yuki771555/2dosui/twodosumi/web.py

from __future__ import annotations

from dataclasses import asdict
import os
from pathlib import Path
import subprocess
import sys
from typing import Any, Callable

from .cli import calibrate_scale_file, calibrate_zero_file
from .config import (
    AppConfig,
    KNOWN_EVENTS,
    ScheduledAlarmConfig,
    Secrets,
    load_config,
    load_secrets,
    save_config,
    save_secrets,
    validate_config,
)
from .notifier import send_test_webhook
from .sensors import check_sensor
from .status import read_status


EDITABLE_CONFIG_FIELDS = {
    "log_path",
    "status_path",
    "person_weight_kg",
    "sample_interval_sec",
    "warmup_samples",
    "median_samples",
    "moving_average_window",
    "exit_ratio",
    "return_ratio",
    "monitor_sec",
    "confirm_sec",
    "data_pin",
    "clock_pin",
    "hx711_ready_timeout_sec",
    "alarm_enabled",
    "buzzer_enabled",
    "buzzer_pin",
    "buzzer_duration_sec",
    "buzzer_pulse_sec",
    "scheduled_alarm_enabled",
    "scheduled_alarms",
    "bed_recheck_minutes",
    "wake_mission_enabled",
    "wake_mission_required_off_bed_sec",
    "webhook_enabled",
    "webhook_events",
    "webhook_payload_format",
    "webhook_timeout_sec",
}


class ProcessManager:
    def __init__(self, config_path: str, secrets_path: str) -> None:
        self.config_path = config_path
        self.secrets_path = secrets_path
        self.process: subprocess.Popen[bytes] | None = None

    def is_running(self) -> bool:
        return self.process is not None and self.process.poll() is None

    def start(self) -> None:
        if self.is_running():
            return
        command = [
            sys.executable,
            "-m",
            "twodosumi",
            "run",
            "--config",
            self.config_path,
            "--secrets",
            self.secrets_path,
        ]
        self.process = subprocess.Popen(command)

    def stop(self) -> None:
        if not self.is_running():
            self.process = None
            return
        assert self.process is not None
        self.process.terminate()
        try:
            self.process.wait(timeout=10)
        except subprocess.TimeoutExpired:
            self.process.kill()
            self.process.wait(timeout=10)
        self.process = None


def _coerce_config_value(field: str, value: Any) -> Any:
    int_fields = {"warmup_samples", "median_samples", "moving_average_window"}
    float_fields = {
        "person_weight_kg",
        "sample_interval_sec",
        "exit_ratio",
        "return_ratio",
        "monitor_sec",
        "confirm_sec",
        "hx711_ready_timeout_sec",
        "buzzer_duration_sec",
        "buzzer_pulse_sec",
        "bed_recheck_minutes",
        "wake_mission_required_off_bed_sec",
        "webhook_timeout_sec",
    }
    bool_fields = {
        "alarm_enabled",
        "buzzer_enabled",
        "scheduled_alarm_enabled",
        "wake_mission_enabled",
        "webhook_enabled",
    }
    list_fields = {"webhook_events"}

    if field in int_fields:
        return int(value)
    if field in float_fields:
        return float(value)
    if field in bool_fields:
        return bool(value)
    if field in list_fields:
        if not isinstance(value, list):
            raise ValueError(f"{field} must be a list")
        return [str(item) for item in value]
    if field == "scheduled_alarms":
        if not isinstance(value, list):
            raise ValueError("scheduled_alarms must be a list")
        return [
            ScheduledAlarmConfig(
                id=str(item.get("id", "")),
                time=str(item.get("time", "07:00")),
                enabled=bool(item.get("enabled", True)),
                label=str(item.get("label", "")),
                weekdays=[int(day) for day in item.get("weekdays", [0, 1, 2, 3, 4, 5, 6])],
            )
            for item in value
            if isinstance(item, dict)
        ]
    return str(value)


def create_app(config_path: str, secrets_path: str):
    try:
        from flask import Flask, jsonify, request
    except ImportError as exc:
        raise RuntimeError("Install Flask first: python3 -m pip install -r requirements-pi.txt") from exc

    app = Flask(__name__)
    manager = ProcessManager(config_path, secrets_path)

    def error_response(message: str, status: int = 400):
        return jsonify({"ok": False, "error": message}), status

    def require_auth(handler: Callable[..., Any]) -> Callable[..., Any]:
        def wrapped(*args: Any, **kwargs: Any) -> Any:
            secrets = load_secrets(secrets_path)
            if not secrets.web_ui_token:
                return error_response("web_ui_token is not configured", 503)
            token = request.headers.get("X-2Dosumi-Token", "")
            if token != secrets.web_ui_token:
                return error_response("unauthorized", 401)
            return handler(*args, **kwargs)

        wrapped.__name__ = handler.__name__
        return wrapped

    @app.get("/")
    def index() -> str:
        return INDEX_HTML

    @app.get("/healthz")
    def healthz():
        return jsonify({"ok": True})

    @app.get("/api/settings")
    @require_auth
    def get_settings():
        config = load_config(config_path)
        secrets = load_secrets(secrets_path)
        data = asdict(config)
        data["webhook_url"] = secrets.webhook_url
        data["web_ui_token_configured"] = bool(secrets.web_ui_token)
        data["known_events"] = sorted(KNOWN_EVENTS)
        return jsonify({"ok": True, "settings": data})

    @app.post("/api/settings")
    @require_auth
    def post_settings():
        payload = request.get_json(force=True, silent=True) or {}
        settings = payload.get("settings", payload)
        if not isinstance(settings, dict):
            return error_response("settings must be an object")

        config = load_config(config_path)
        secrets = load_secrets(secrets_path)
        for field, value in settings.items():
            if field in EDITABLE_CONFIG_FIELDS:
                setattr(config, field, _coerce_config_value(field, value))
            elif field == "webhook_url":
                secrets.webhook_url = str(value)
            elif field == "web_ui_token" and value:
                secrets.web_ui_token = str(value)

        errors = validate_config(config)
        if errors:
            return error_response("; ".join(errors))
        was_running = manager.is_running()
        if was_running:
            manager.stop()
        save_config(config_path, config)
        save_secrets(secrets_path, secrets)
        if was_running:
            manager.start()
        return jsonify({"ok": True, "restarted": was_running})

    @app.get("/api/status")
    @require_auth
    def get_status():
        config = load_config(config_path)
        status = read_status(config.status_path)
        status["managed_process_running"] = manager.is_running()
        return jsonify({"ok": True, "status": status})

    @app.post("/api/run/start")
    @require_auth
    def start_run():
        manager.start()
        return jsonify({"ok": True, "running": manager.is_running()})

    @app.post("/api/run/stop")
    @require_auth
    def stop_run():
        manager.stop()
        return jsonify({"ok": True, "running": manager.is_running()})

    @app.post("/api/calibration/zero")
    @require_auth
    def calibrate_zero():
        was_running = manager.is_running()
        if was_running:
            manager.stop()
        try:
            payload = request.get_json(force=True, silent=True) or {}
            samples = int(payload.get("samples", 30))
            zero = calibrate_zero_file(config_path, samples)
        finally:
            if was_running:
                manager.start()
        return jsonify({"ok": True, "zero_offset": zero, "restarted": was_running})

    @app.post("/api/calibration/scale")
    @require_auth
    def calibrate_scale():
        was_running = manager.is_running()
        if was_running:
            manager.stop()
        try:
            payload = request.get_json(force=True, silent=True) or {}
            samples = int(payload.get("samples", 30))
            known_kg = float(payload.get("known_kg", 0))
            scale = calibrate_scale_file(config_path, known_kg, samples)
        finally:
            if was_running:
                manager.start()
        return jsonify({"ok": True, "scale_factor": scale, "restarted": was_running})

    @app.post("/api/sensor/check")
    @require_auth
    def sensor_check():
        was_running = manager.is_running()
        if was_running:
            manager.stop()
        try:
            payload = request.get_json(force=True, silent=True) or {}
            samples = int(payload.get("samples", 10))
            interval_sec = float(payload.get("interval_sec", 0.1))
            config = load_config(config_path)
            errors = validate_config(config)
            if errors:
                return error_response("; ".join(errors))
            result = check_sensor(config, samples=samples, interval_sec=interval_sec)
        finally:
            if was_running:
                manager.start()
        return jsonify({"ok": True, "sensor": asdict(result), "restarted": was_running})

    @app.post("/api/test-webhook")
    @require_auth
    def test_webhook():
        config = load_config(config_path)
        secrets = load_secrets(secrets_path)
        if not secrets.webhook_url:
            return error_response("webhook_url is not configured")
        send_test_webhook(config, secrets)
        return jsonify({"ok": True})

    return app


def ensure_secrets_file(path: str) -> None:
    target = Path(path)
    if target.exists():
        return
    token = os.urandom(12).hex()
    save_secrets(target, Secrets(web_ui_token=token))
    print(f"Created {target} with web_ui_token={token}", flush=True)


def run_web(config_path: str, secrets_path: str, host: str, port: int) -> None:
    ensure_secrets_file(secrets_path)
    app = create_app(config_path, secrets_path)
    print(f"Open http://{host}:{port}", flush=True)
    app.run(host=host, port=port)


INDEX_HTML = r"""<!doctype html>
<html lang="ja">
<head>
  <meta charset="utf-8">
  <meta name="viewport" content="width=device-width, initial-scale=1">
  <title>2dosumi</title>
  <style>
    :root {
      color-scheme: light;
      font-family: -apple-system, BlinkMacSystemFont, "SF Pro Text", "SF Pro Display", "Segoe UI", system-ui, sans-serif;
      --bg: #f2f2f7;
      --panel: #ffffff;
      --panel-soft: #f2f2f7;
      --panel-glass: rgba(255, 255, 255, 0.78);
      --bar-glass: rgba(248, 248, 248, 0.86);
      --ink: #1d1d1f;
      --muted: #6e6e73;
      --line: rgba(60, 60, 67, 0.18);
      --accent: #007aff;
      --accent-dark: #005ecb;
      --accent-soft: rgba(0, 122, 255, 0.11);
      --good: #34c759;
      --warn: #ff3b30;
      --blue: #007aff;
      --on-accent: #ffffff;
      --shadow: 0 22px 48px rgba(0, 0, 0, 0.08);
      --button-shadow: none;
      --hero-bg: linear-gradient(180deg, rgba(255, 255, 255, 0.96), rgba(255, 255, 255, 0.82));
      --status-bg: #101828;
      --status-ink: #eef4ff;
      --surface-shadow: 0 1px 0 rgba(0, 0, 0, 0.03), 0 10px 30px rgba(0, 0, 0, 0.04);
      --segment-bg: rgba(118, 118, 128, 0.12);
      --segment-active: rgba(255, 255, 255, 0.96);
    }
    [data-theme="dark"] {
      color-scheme: dark;
      --bg: #000000;
      --panel: #1c1c1e;
      --panel-soft: #2c2c2e;
      --panel-glass: rgba(28, 28, 30, 0.82);
      --bar-glass: rgba(28, 28, 30, 0.84);
      --ink: #f5f5f7;
      --muted: #a1a1a6;
      --line: rgba(84, 84, 88, 0.58);
      --accent: #0a84ff;
      --accent-dark: #64b5ff;
      --accent-soft: rgba(10, 132, 255, 0.18);
      --good: #30d158;
      --warn: #ff453a;
      --blue: #0a84ff;
      --on-accent: #ffffff;
      --shadow: 0 24px 58px rgba(0, 0, 0, 0.5);
      --button-shadow: none;
      --hero-bg: linear-gradient(180deg, rgba(28, 28, 30, 0.96), rgba(28, 28, 30, 0.84));
      --status-bg: #111113;
      --status-ink: #f5f5f7;
      --surface-shadow: 0 1px 0 rgba(255, 255, 255, 0.04), 0 12px 34px rgba(0, 0, 0, 0.22);
      --segment-bg: rgba(118, 118, 128, 0.24);
      --segment-active: rgba(99, 99, 102, 0.86);
    }
    * { box-sizing: border-box; }
    [hidden] { display: none !important; }
    html { scroll-behavior: smooth; }
    body {
      min-height: 100vh;
      margin: 0;
      background: var(--bg);
      color: var(--ink);
      transition: background 260ms ease, color 260ms ease;
    }
    main { width: min(100%, 1180px); margin: 0 auto; padding: 18px; }
    h1, h2 { margin: 0; letter-spacing: 0; }
    h1 { font-size: clamp(30px, 5vw, 48px); line-height: 0.98; }
    h2 { font-size: 16px; }
    p { margin: 0; }
    a, button, input, select, strong, span { min-width: 0; }
    button { outline: none; }
    button:focus-visible, input:focus-visible, select:focus-visible {
      outline: 3px solid color-mix(in srgb, var(--accent) 32%, transparent);
      outline-offset: 2px;
    }
    .app-frame {
      position: relative;
      overflow: clip;
      border: 1px solid var(--line);
      border-radius: 18px;
      background: var(--panel-glass);
      box-shadow: var(--shadow);
      backdrop-filter: blur(28px) saturate(1.6);
      transition: background 260ms ease, border-color 260ms ease, box-shadow 260ms ease;
    }
    .app-frame::before { content: none; }
    .app-bar {
      position: relative;
      z-index: 1;
      display: flex;
      justify-content: space-between;
      align-items: center;
      gap: 12px;
      min-height: 64px;
      padding: 0 20px;
      border-bottom: 1px solid var(--line);
      background: var(--bar-glass);
      backdrop-filter: blur(24px) saturate(1.45);
    }
    .brand { display: flex; align-items: center; gap: 10px; min-width: 0; }
    .brand-mark {
      width: 34px;
      height: 34px;
      border-radius: 10px;
      background: linear-gradient(145deg, #5ac8fa, var(--accent));
      box-shadow: inset 0 1px 0 rgba(255, 255, 255, 0.46);
    }
    .brand-text { display: grid; gap: 2px; min-width: 0; }
    .brand strong { font-size: 17px; font-weight: 900; }
    .brand span { color: var(--muted); font-size: 12px; font-weight: 750; }
    .app-tools { display: flex; align-items: center; justify-content: flex-end; gap: 8px; min-width: 0; }
    .content { position: relative; z-index: 1; padding: 12px; }
    .tab-bar {
      position: sticky;
      top: 0;
      z-index: 4;
      display: flex;
      gap: 2px;
      padding: 3px;
      margin-bottom: 10px;
      overflow-x: auto;
      border: 0;
      border-radius: 12px;
      background: var(--segment-bg);
      backdrop-filter: blur(18px) saturate(1.45);
      scrollbar-width: none;
    }
    .tab-bar::-webkit-scrollbar { display: none; }
    .tab-button {
      display: inline-grid;
      grid-template-columns: auto auto;
      place-items: center;
      gap: 7px;
      flex: 1 1 0;
      min-width: 0;
      min-height: 44px;
      padding: 8px 14px;
      border: 0;
      border-radius: 10px;
      background: transparent;
      color: var(--muted);
      box-shadow: none;
      font-size: 13px;
      font-weight: 760;
      transition: background 180ms ease, color 180ms ease, box-shadow 180ms ease, transform 180ms ease;
    }
    .tab-button:hover { transform: none; background: color-mix(in srgb, var(--segment-active) 68%, transparent); box-shadow: none; }
    .tab-button.active {
      background: var(--segment-active);
      color: var(--ink);
      box-shadow: 0 2px 7px rgba(0, 0, 0, 0.13);
    }
    .tab-button.active .tab-icon { transform: scale(1.08); }
    .tab-icon { transition: transform 180ms cubic-bezier(.2, .9, .2, 1); }
    .theme-toggle {
      display: inline-flex;
      align-items: center;
      gap: 7px;
      min-height: 44px;
      padding: 7px 11px;
      border: 0;
      border-radius: 999px;
      background: var(--segment-bg);
      color: var(--ink);
      box-shadow: none;
      white-space: nowrap;
      backdrop-filter: blur(16px) saturate(1.35);
    }
    .theme-toggle:hover { transform: none; background: color-mix(in srgb, var(--segment-active) 72%, transparent); box-shadow: none; }
    .tab-icon { font-size: 14px; line-height: 1; }
    body:not([data-tab="overview"]) .hero { display: none; }
    .hero {
      display: grid;
      grid-template-columns: minmax(0, 1.3fr) minmax(min(100%, 220px), 0.7fr);
      gap: 14px;
      overflow: hidden;
      padding: 22px;
      border: 1px solid var(--line);
      border-radius: 18px;
      background: var(--hero-bg);
      box-shadow: var(--surface-shadow);
    }
    .hero-main { display: flex; flex-direction: column; gap: 16px; min-width: 0; }
    .hero-kicker {
      width: fit-content;
      padding: 5px 10px;
      border: 1px solid color-mix(in srgb, var(--accent) 22%, var(--line));
      border-radius: 999px;
      background: var(--accent-soft);
      color: var(--accent-dark);
      font-size: 12px;
      font-weight: 850;
    }
    .hero-state { display: flex; align-items: center; gap: 12px; flex-wrap: wrap; }
    .state-badge {
      display: inline-flex; align-items: center; gap: 9px;
      padding: 10px 18px;
      border-radius: 999px;
      font-size: clamp(20px, 3.4vw, 30px);
      font-weight: 900; line-height: 1;
      border: 1px solid var(--line);
      background: var(--panel);
      color: var(--ink);
      transition: color 200ms ease, background 200ms ease, border-color 200ms ease;
    }
    .state-badge::before {
      content: ""; width: 12px; height: 12px; border-radius: 50%;
      background: currentColor; box-shadow: 0 0 0 4px color-mix(in srgb, currentColor 22%, transparent);
    }
    .state-badge.state-idle  { color: var(--muted); }
    .state-badge.state-sleep { color: var(--accent); border-color: color-mix(in srgb, var(--accent) 40%, var(--line)); background: var(--accent-soft); }
    .state-badge.state-watch { color: #ff9f0a; border-color: color-mix(in srgb, #ff9f0a 40%, var(--line)); background: color-mix(in srgb, #ff9f0a 13%, var(--panel)); }
    .state-badge.state-alert { color: var(--warn); border-color: color-mix(in srgb, var(--warn) 40%, var(--line)); background: color-mix(in srgb, var(--warn) 13%, var(--panel)); }
    .state-badge.state-done  { color: var(--good); border-color: color-mix(in srgb, var(--good) 40%, var(--line)); background: color-mix(in srgb, var(--good) 13%, var(--panel)); }
    .hero-updated { color: var(--muted); font-size: 13px; font-weight: 700; }
    .hero-weight-wrap { display: flex; align-items: baseline; gap: 10px; flex-wrap: wrap; }
    .hero-weight-label { color: var(--muted); font-size: 13px; font-weight: 800; }
    .hero-weight-wrap strong { font-size: clamp(34px, 6vw, 52px); line-height: 1; font-weight: 900; overflow-wrap: anywhere; }
    .hero-mission { display: grid; gap: 8px; padding: 12px 14px; border: 1px solid color-mix(in srgb, #ff9f0a 30%, var(--line)); border-radius: 14px; background: color-mix(in srgb, #ff9f0a 10%, var(--panel)); }
    .mission-head { display: flex; justify-content: space-between; gap: 10px; font-size: 13px; font-weight: 850; }
    .mission-track { height: 8px; border-radius: 999px; background: color-mix(in srgb, var(--muted) 24%, transparent); overflow: hidden; }
    .mission-bar { height: 100%; width: 0%; border-radius: 999px; background: linear-gradient(90deg, #ff9f0a, var(--good)); transition: width 320ms ease; }
    .hero-controls { display: grid; align-content: start; gap: 10px; }
    button.big { min-height: 52px; font-size: 16px; font-weight: 850; }
    button.ghost { background: var(--segment-bg); color: var(--ink); box-shadow: none; }
    button.ghost:hover { background: color-mix(in srgb, var(--segment-active) 72%, transparent); filter: none; }
    .auto-indicator { display: inline-flex; align-items: center; gap: 7px; justify-content: center; color: var(--muted); font-size: 12px; font-weight: 750; }
    .live-dot { width: 8px; height: 8px; border-radius: 50%; background: var(--good); animation: livePulse 2s ease-out infinite; }
    @keyframes livePulse {
      0% { box-shadow: 0 0 0 0 color-mix(in srgb, var(--good) 55%, transparent); }
      70% { box-shadow: 0 0 0 7px transparent; }
      100% { box-shadow: 0 0 0 0 transparent; }
    }
    .alarm-card {
      display: flex;
      justify-content: space-between;
      align-items: center;
      gap: 14px;
      padding: 15px;
      border: 1px solid var(--line);
      border-radius: 14px;
      background: var(--panel);
      transition: transform 180ms ease, border-color 180ms ease, box-shadow 180ms ease, background 260ms ease;
    }
    .alarm-card:hover { transform: translateY(-1px); border-color: color-mix(in srgb, var(--accent) 22%, var(--line)); box-shadow: var(--surface-shadow); }
    .alarm-card strong { display: block; font-size: 15px; }
    .alarm-card span { display: block; margin-top: 3px; color: var(--muted); font-size: 12px; line-height: 1.45; }
    .alarm-preview-list { display: grid; gap: 8px; margin-top: 10px; }
    .alarm-preview-item {
      display: grid;
      grid-template-columns: auto minmax(0, 1fr) auto;
      gap: 10px;
      align-items: center;
      padding: 12px;
      border: 1px solid var(--line);
      border-radius: 13px;
      background: var(--panel);
      transition: transform 180ms ease, border-color 180ms ease, box-shadow 180ms ease;
    }
    .alarm-preview-item:hover { transform: none; border-color: color-mix(in srgb, var(--blue) 24%, var(--line)); box-shadow: var(--surface-shadow); }
    .alarm-preview-time { font-size: 22px; font-weight: 900; white-space: nowrap; }
    .alarm-preview-meta { display: grid; gap: 2px; min-width: 0; }
    .alarm-preview-meta strong { overflow-wrap: anywhere; }
    .alarm-preview-meta span { color: var(--muted); font-size: 12px; overflow-wrap: anywhere; }
    .link-button {
      display: grid;
      place-items: center;
      min-height: 44px;
      margin-top: 10px;
      width: 100%;
      border: 0;
      border-radius: 12px;
      background: var(--segment-bg);
      color: var(--blue);
      font-weight: 850;
      text-decoration: none;
      box-shadow: none;
    }
    .link-button:hover { transform: none; background: var(--accent-soft); box-shadow: none; }
    .switch {
      position: relative;
      display: inline-flex;
      width: 52px;
      min-width: 52px;
      height: 32px;
    }
    .switch input { position: absolute; inset: 0; z-index: 2; width: 100%; height: 100%; margin: 0; opacity: 0; cursor: pointer; }
    .slider {
      position: absolute;
      inset: 0;
      border-radius: 999px;
      background: #e9e9eb;
      transition: background 160ms ease;
      cursor: pointer;
    }
    [data-theme="dark"] .slider { background: #39393d; }
    .slider::after {
      content: "";
      position: absolute;
      width: 28px;
      height: 28px;
      top: 2px;
      left: 2px;
      border-radius: 50%;
      background: #fff;
      box-shadow: 0 3px 8px rgba(0, 0, 0, 0.22);
      transition: transform 180ms cubic-bezier(.2, .9, .2, 1), box-shadow 180ms ease;
    }
    .switch input:checked + .slider { background: var(--good); }
    .switch input:checked + .slider::after { transform: translateX(20px); }
    .top-actions { display: grid; grid-template-columns: repeat(auto-fit, minmax(min(100%, 150px), 1fr)); gap: 10px; align-items: center; }
    .tab-panels { display: grid; margin-top: 12px; }
    .tab-panel { display: none; }
    .tab-panel.active { display: grid; gap: 12px; animation: panelIn 260ms ease both; }
    .overview-grid { display: grid; grid-template-columns: minmax(280px, 0.76fr) minmax(0, 1.24fr); gap: 12px; align-items: start; }
    .overview-sidebar { display: grid; gap: 12px; }
    .overview-status { min-height: 100%; }
    section {
      background: var(--panel-glass);
      border: 1px solid var(--line);
      border-radius: 16px;
      padding: 16px;
      box-shadow: var(--surface-shadow);
      transition: transform 180ms ease, border-color 180ms ease, box-shadow 180ms ease, background 260ms ease;
    }
    section:hover { border-color: color-mix(in srgb, var(--accent) 14%, var(--line)); box-shadow: var(--surface-shadow); }
    section, .setting-group, .alarm-card, .metric, .live-card { min-width: 0; }
    section { scroll-margin-top: 82px; }
    .stack { display: grid; gap: 14px; align-content: start; }
    .section-head { display: flex; justify-content: space-between; gap: 12px; align-items: center; margin-bottom: 14px; }
    .section-head.sticky {
      position: sticky;
      top: 61px;
      z-index: 3;
      margin: -16px -16px 14px;
      padding: 14px 16px;
      border-bottom: 1px solid var(--line);
      background: var(--bar-glass);
      backdrop-filter: blur(16px);
    }
    .grid { display: grid; grid-template-columns: repeat(auto-fit, minmax(min(100%, 184px), 1fr)); gap: 12px; }
    .settings-grid { grid-template-columns: repeat(auto-fit, minmax(min(100%, 260px), 1fr)); }
    .setting-group {
      display: grid;
      gap: 12px;
      padding: 14px;
      border: 1px solid var(--line);
      border-radius: 14px;
      background: var(--panel);
      transition: transform 180ms ease, border-color 180ms ease, box-shadow 180ms ease, background 260ms ease;
    }
    .setting-group:hover { transform: none; border-color: color-mix(in srgb, var(--blue) 16%, var(--line)); box-shadow: var(--surface-shadow); }
    .setting-group.wide { grid-column: 1 / -1; }
    .setting-group h3 {
      margin: 0;
      padding-bottom: 8px;
      border-bottom: 1px solid var(--line);
      font-size: 15px;
      letter-spacing: 0;
    }
    .setting-group-fields { display: grid; grid-template-columns: repeat(auto-fit, minmax(min(100%, 190px), 1fr)); gap: 12px; }
    .scheduled-editor { display: grid; gap: 12px; grid-column: 1 / -1; }
    .scheduled-row {
      display: grid;
      grid-template-columns: minmax(170px, 0.8fr) minmax(220px, 1.2fr) minmax(88px, auto);
      gap: 12px;
      align-items: center;
      padding: 14px;
      border: 1px solid var(--line);
      border-radius: 14px;
      background: var(--panel);
      overflow: hidden;
    }
    .scheduled-time-block { display: flex; align-items: center; gap: 13px; min-width: 0; flex-wrap: wrap; }
    .scheduled-time-block .scheduled-time {
      min-height: 54px;
      padding: 6px 8px;
      border: 0;
      background: transparent;
      color: var(--ink);
      width: 132px;
      font-size: 28px;
      font-weight: 850;
    }
    .scheduled-detail { display: grid; gap: 9px; min-width: 0; }
    .scheduled-detail .scheduled-label {
      min-height: 38px;
      border-radius: 11px;
      background: var(--panel-soft);
    }
    .weekday-row { display: flex; flex-wrap: wrap; gap: 6px; align-items: center; min-width: 0; }
    .weekday-row label {
      position: relative;
      display: inline-flex;
      align-items: center;
      gap: 4px;
      min-height: 34px;
      padding: 4px 9px;
      border: 1px solid var(--line);
      border-radius: 999px;
      background: var(--panel-soft);
      color: var(--ink);
      font-size: 12px;
      font-weight: 800;
    }
    .weekday-row input {
      position: absolute;
      width: 1px;
      min-height: 1px;
      opacity: 0;
      pointer-events: none;
    }
    .weekday-row label:has(input) { cursor: pointer; }
    .weekday-row label:has(input:checked) {
      border-color: color-mix(in srgb, var(--good) 34%, var(--line));
      background: color-mix(in srgb, var(--good) 14%, var(--panel));
      color: var(--good);
    }
    label { display: grid; gap: 6px; font-size: 12px; color: var(--muted); font-weight: 650; min-width: 0; }
    input, select {
      width: 100%;
      min-height: 44px;
      font: inherit;
      padding: 9px 10px;
      border: 1px solid var(--line);
      border-radius: 11px;
      background: color-mix(in srgb, var(--panel) 88%, transparent);
      color: var(--ink);
      outline: none;
      transition: border-color 160ms ease, box-shadow 160ms ease, background 260ms ease;
    }
    input:focus, select:focus { border-color: var(--accent); box-shadow: 0 0 0 3px color-mix(in srgb, var(--accent) 18%, transparent); }
    input[type="checkbox"] { width: 20px; min-height: 20px; accent-color: var(--good); }
    input[type="time"] { min-width: 0; }
    button {
      min-height: 44px;
      font: inherit;
      font-weight: 750;
      padding: 9px 13px;
      border: 0;
      border-radius: 11px;
      background: var(--accent);
      color: var(--on-accent);
      cursor: pointer;
      box-shadow: var(--button-shadow);
      transition: transform 140ms ease, box-shadow 140ms ease, filter 140ms ease, background 140ms ease;
    }
    button:hover { transform: none; filter: brightness(0.97); box-shadow: none; }
    button:active { transform: translateY(1px); box-shadow: var(--button-shadow); }
    button.secondary { background: var(--segment-bg); color: var(--blue); box-shadow: none; }
    button.secondary:hover { box-shadow: none; }
    button.warn { background: var(--warn); color: var(--on-accent); box-shadow: none; }
    button.warn:hover { box-shadow: none; }
    .actions { display: flex; flex-wrap: wrap; gap: 8px; align-items: center; min-width: 0; }
    .actions button { flex: 1 1 150px; }
    .status-cards { display: grid; grid-template-columns: repeat(auto-fit, minmax(min(100%, 140px), 1fr)); gap: 10px; margin-bottom: 12px; }
    .metric {
      position: relative;
      overflow: hidden;
      background: var(--panel);
      border: 1px solid var(--line);
      border-radius: 14px;
      padding: 13px;
      min-height: 78px;
      transition: transform 180ms ease, border-color 180ms ease, box-shadow 180ms ease, background 260ms ease;
    }
    .metric:hover { transform: translateY(-1px); box-shadow: var(--surface-shadow); }
    .metric::before {
      content: "";
      position: absolute;
      inset: 0 0 auto;
      height: 2px;
      background: var(--accent);
    }
    .metric span { display: block; color: var(--muted); font-size: 12px; font-weight: 700; }
    .metric strong { display: block; margin-top: 5px; font-size: 20px; overflow-wrap: anywhere; }
    .pill {
      display: inline-flex;
      align-items: center;
      min-height: 28px;
      padding: 4px 11px;
      border: 1px solid rgba(26, 117, 91, 0.18);
      border-radius: 999px;
      font-size: 12px;
      font-weight: 850;
      background: color-mix(in srgb, var(--good) 14%, var(--panel));
      color: var(--good);
      white-space: nowrap;
    }
    .pill.off { border-color: color-mix(in srgb, var(--warn) 20%, var(--line)); background: color-mix(in srgb, var(--warn) 10%, var(--panel)); color: var(--warn); }
    [data-theme="dark"] .pill { border-color: rgba(76, 217, 100, 0.24); background: rgba(76, 217, 100, 0.14); }
    [data-theme="dark"] .pill.off { border-color: rgba(255, 105, 97, 0.24); background: rgba(255, 105, 97, 0.14); }
    .status {
      max-height: 260px;
      overflow: auto;
      white-space: pre-wrap;
      font-family: ui-monospace, SFMono-Regular, Consolas, monospace;
      font-size: 12px;
      line-height: 1.55;
      margin: 0;
      padding: 12px;
      border-radius: 14px;
      background: var(--status-bg);
      color: var(--status-ink);
    }
    .sensor-check-result {
      display: grid;
      gap: 8px;
      margin-top: 12px;
      padding: 12px;
      border: 1px solid var(--line);
      border-radius: 14px;
      background: var(--panel-soft);
      color: var(--ink);
      font-size: 13px;
      line-height: 1.5;
      overflow-wrap: anywhere;
    }
    .sensor-check-result.ok { border-color: color-mix(in srgb, var(--good) 28%, var(--line)); background: color-mix(in srgb, var(--good) 9%, var(--panel)); }
    .sensor-check-result.fail { border-color: color-mix(in srgb, var(--warn) 28%, var(--line)); background: color-mix(in srgb, var(--warn) 9%, var(--panel)); }
    [data-theme="dark"] .sensor-check-result.ok { background: rgba(76, 217, 100, 0.12); }
    [data-theme="dark"] .sensor-check-result.fail { background: rgba(255, 105, 97, 0.12); }
    .message {
      position: sticky;
      bottom: 12px;
      z-index: 2;
      min-height: 28px;
      margin: 14px 0 0;
      padding: 8px 12px;
      border-radius: 14px;
      background: rgba(23, 33, 43, 0.92);
      color: white;
      font-weight: 750;
      opacity: 0;
      transform: translateY(8px) scale(0.985);
      transition: opacity 180ms ease, transform 220ms cubic-bezier(.2, .9, .2, 1);
    }
    .message.show { opacity: 1; transform: translateY(0) scale(1); }
    .full { grid-column: 1 / -1; }
    @keyframes panelIn {
      from { opacity: 0; transform: translateY(8px) scale(0.995); }
      to { opacity: 1; transform: translateY(0) scale(1); }
    }
    @media (prefers-reduced-motion: reduce) {
      *, *::before, *::after {
        animation-duration: 0.001ms !important;
        animation-iteration-count: 1 !important;
        scroll-behavior: auto !important;
        transition-duration: 0.001ms !important;
      }
    }
    @media (max-width: 980px) {
      .overview-grid { grid-template-columns: 1fr; }
      .scheduled-row { grid-template-columns: minmax(0, 1fr); align-items: stretch; }
      .scheduled-row .warn { width: 100%; }
    }
    @media (max-width: 820px) {
      main { padding: 10px; }
      .content { padding: 10px; }
      .app-bar { min-height: 54px; padding: 0 12px; }
      .brand-text span { display: none; }
      .brand-mark { width: 30px; height: 30px; }
      .theme-toggle { padding: 7px 9px; }
      .hero { grid-template-columns: 1fr; min-height: 0; }
      .hero-copy { padding: 20px; }
      .hero-panel { padding: 0 20px 20px; }
      .live-card { min-height: 122px; }
      .top-actions { grid-template-columns: 1fr 1fr; }
      .top-actions .secondary { grid-column: 1 / -1; }
      button { flex: 1 1 132px; }
      .alarm-card { align-items: flex-start; }
      .section-head.sticky { top: 55px; }
    }
    @media (max-width: 520px) {
      main { padding: 0; }
      .app-frame { border-radius: 0; border-left: 0; border-right: 0; }
      .tab-bar {
        display: grid;
        grid-template-columns: repeat(4, minmax(0, 1fr));
        border-left: 0;
        border-right: 0;
        border-radius: 0;
        overflow: visible;
      }
      .tab-button { padding: 8px 6px; gap: 4px; font-size: 12px; }
      .hero-copy { padding: 18px; }
      .hero-panel { padding: 0 18px 18px; }
      .top-actions { grid-template-columns: 1fr; }
      .section-head, .alarm-card { align-items: stretch; flex-direction: column; }
      .section-head .pill { align-self: flex-start; }
      .section-head.sticky {
        position: static;
        top: auto;
      }
      .section-head.sticky .actions { width: 100%; }
      .scheduled-time-block { justify-content: space-between; }
      .scheduled-time-block .scheduled-time { flex: 1; font-size: 26px; }
      .status { max-height: 190px; }
    }
    @media (max-width: 380px) {
      .tab-icon { display: none; }
      .tab-button { font-size: 12px; }
      .theme-toggle span:last-child { display: none; }
      section { padding: 13px; }
      .section-head.sticky { margin: -13px -13px 13px; padding: 13px; }
    }
    .chip-button { cursor: pointer; }
    .connect-card { border-color: color-mix(in srgb, var(--accent) 32%, var(--line)); }
    .connect-hint { color: var(--muted); font-size: 13px; margin-bottom: 12px; line-height: 1.55; }
    .connect-row { display: flex; gap: 8px; flex-wrap: wrap; align-items: center; }
    .connect-row input { flex: 1 1 200px; }
    .connect-row button { flex: 0 0 auto; }
    .alarm-summary { padding: 2px 0 4px; }
    .alarm-summary strong { font-size: 15px; font-weight: 800; overflow-wrap: anywhere; }
    .status-details { margin-top: 12px; }
    .status-details summary {
      cursor: pointer; color: var(--muted); font-size: 12px; font-weight: 800;
      padding: 6px 0; list-style: none; user-select: none;
    }
    .status-details summary::-webkit-details-marker { display: none; }
    .status-details summary::before { content: "\25B8  "; }
    .status-details[open] summary::before { content: "\25BE  "; }
    .status-details .status { margin-top: 8px; }

    /* --- settings help & advanced --- */
    .field-help { color: var(--muted); font-size: 11px; font-weight: 600; line-height: 1.4; }
    .group-desc { margin: -4px 0 4px; color: var(--muted); font-size: 12px; line-height: 1.45; }
    .group-advanced { grid-column: 1 / -1; margin-top: 2px; }
    .group-advanced > summary {
      cursor: pointer; color: var(--blue); font-size: 12px; font-weight: 800;
      padding: 8px 0; list-style: none; user-select: none; min-height: 40px;
      display: flex; align-items: center;
    }
    .group-advanced > summary::-webkit-details-marker { display: none; }
    .group-advanced > summary::before { content: "\25B8\00a0\00a0"; }
    .group-advanced[open] > summary::before { content: "\25BE\00a0\00a0"; }
    .group-advanced .setting-group-fields { margin-top: 8px; }

    /* --- busy / disabled buttons --- */
    button:disabled { opacity: 0.6; cursor: progress; filter: none; transform: none; }
    .spinner {
      display: inline-block; width: 14px; height: 14px; margin-right: 7px;
      vertical-align: -2px; border-radius: 50%;
      border: 2px solid color-mix(in srgb, currentColor 30%, transparent);
      border-top-color: currentColor; animation: spin 0.7s linear infinite;
    }
    @keyframes spin { to { transform: rotate(360deg); } }

    /* --- toast variants --- */
    .message.ok { background: color-mix(in srgb, var(--good) 88%, #0b3d1f); }
    .message.error { background: color-mix(in srgb, var(--warn) 90%, #4a0f0b); }

    /* --- metric tone bar --- */
    .metric[data-tone="sleep"]::before { background: var(--accent); }
    .metric[data-tone="watch"]::before { background: #ff9f0a; }
    .metric[data-tone="alert"]::before { background: var(--warn); }
    .metric[data-tone="done"]::before { background: var(--good); }
    .metric[data-tone="idle"]::before { background: color-mix(in srgb, var(--muted) 60%, transparent); }

    /* --- weight sparkline --- */
    .hero-trend { margin-top: 4px; }
    .hero-trend.empty { display: none; }
    .sparkline { display: block; width: 100%; height: 56px; overflow: visible; }
    .sparkline-line { fill: none; stroke: var(--accent); stroke-width: 2; stroke-linejoin: round; stroke-linecap: round; }
    .sparkline-area { fill: var(--accent-soft); stroke: none; }
    .sparkline-dot { fill: var(--accent); }
    .trend-caption { margin-top: 2px; color: var(--muted); font-size: 11px; font-weight: 650; }

    /* --- event timeline --- */
    .timeline { display: grid; gap: 0; margin-top: 4px; }
    .timeline-empty { color: var(--muted); font-size: 13px; padding: 6px 2px; }
    .event-item {
      display: grid; grid-template-columns: auto minmax(0, 1fr) auto; gap: 10px;
      align-items: center; padding: 9px 2px; border-bottom: 1px solid var(--line);
    }
    .event-item:last-child { border-bottom: 0; }
    .event-dot {
      width: 9px; height: 9px; border-radius: 50%; background: var(--muted);
      box-shadow: 0 0 0 3px color-mix(in srgb, currentColor 18%, transparent);
    }
    .event-dot.tone-sleep { background: var(--accent); color: var(--accent); }
    .event-dot.tone-watch { background: #ff9f0a; color: #ff9f0a; }
    .event-dot.tone-alert { background: var(--warn); color: var(--warn); }
    .event-dot.tone-done { background: var(--good); color: var(--good); }
    .event-label { font-size: 13px; font-weight: 750; overflow-wrap: anywhere; }
    .event-time { color: var(--muted); font-size: 12px; font-weight: 700; white-space: nowrap; }

    /* --- mobile sticky save bar --- */
    .mobile-save-bar { display: none; }
    @media (max-width: 820px) {
      .hero-controls { grid-template-columns: 1fr 1fr; }
      .hero-controls .ghost, .hero-controls .auto-indicator { grid-column: 1 / -1; }
      body[data-tab="settings"] .mobile-save-bar {
        display: flex; gap: 8px;
        position: sticky; bottom: 0; z-index: 5;
        margin: 12px -10px -10px; padding: 10px;
        border-top: 1px solid var(--line);
        background: var(--bar-glass);
        backdrop-filter: blur(18px) saturate(1.4);
      }
      .mobile-save-bar button { flex: 1 1 0; }
      body[data-tab="settings"] .section-head.sticky .actions { display: none; }
    }
    @media (max-width: 520px) {
      .setting-group-fields { grid-template-columns: 1fr; }
      .weekday-row { gap: 8px; }
      .weekday-row label { padding: 6px 11px; min-height: 38px; }
      .event-item { grid-template-columns: auto minmax(0, 1fr) auto; }
    }
  </style>
</head>
<body>
<main>
  <div class="app-frame">
    <div class="app-bar">
      <div class="brand">
        <span class="brand-mark" aria-hidden="true"></span>
        <span class="brand-text"><strong>2dosumi</strong><span>ベッドセンサー管理</span></span>
      </div>
      <div class="app-tools">
        <button id="auth-chip" class="pill off chip-button" type="button" onclick="showConnect()">未認証</button>
        <button id="theme-toggle" class="theme-toggle" type="button" onclick="toggleTheme()" aria-label="ダークモード切り替え"><span id="theme-icon">☀</span><span id="theme-label">Light</span></button>
        <span id="run-pill" class="pill off">停止中</span>
      </div>
    </div>
    <div class="content">
      <nav class="tab-bar" aria-label="画面切り替え">
        <button class="tab-button active" type="button" data-tab="overview" aria-selected="true"><span class="tab-icon">●</span>概要</button>
        <button class="tab-button" type="button" data-tab="alarms" aria-selected="false"><span class="tab-icon">◐</span>アラーム</button>
        <button class="tab-button" type="button" data-tab="calibration" aria-selected="false"><span class="tab-icon">◇</span>校正</button>
        <button class="tab-button" type="button" data-tab="settings" aria-selected="false"><span class="tab-icon">□</span>設定</button>
      </nav>
      <header class="hero">
        <div class="hero-main">
          <p class="hero-kicker">Raspberry Pi 二度寝モニター</p>
          <div class="hero-state">
            <span id="hero-state-badge" class="state-badge state-idle">未取得</span>
            <span id="hero-updated" class="hero-updated">更新待ち</span>
          </div>
          <div class="hero-weight-wrap">
            <span class="hero-weight-label">平滑重量</span>
            <strong id="hero-weight">-</strong>
          </div>
          <div id="hero-trend" class="hero-trend empty">
            <svg id="sparkline" class="sparkline" viewBox="0 0 300 56" preserveAspectRatio="none" aria-hidden="true">
              <polyline id="sparkline-area" class="sparkline-area" points=""></polyline>
              <polyline id="sparkline-line" class="sparkline-line" points=""></polyline>
              <circle id="sparkline-dot" class="sparkline-dot" r="3" cx="0" cy="0" hidden></circle>
            </svg>
            <p class="trend-caption" id="trend-caption">重量の推移（直近）</p>
          </div>
          <div id="hero-mission" class="hero-mission" hidden>
            <div class="mission-head"><span id="hero-mission-label">起床ミッション</span><span id="hero-mission-value"></span></div>
            <div class="mission-track"><div id="hero-mission-bar" class="mission-bar"></div></div>
          </div>
        </div>
        <div class="hero-controls">
          <button class="big" onclick="post('/api/run/start')">検知開始</button>
          <button class="big warn" onclick="post('/api/run/stop')">検知停止</button>
          <button class="ghost" type="button" onclick="loadStatus()">↻ 状態を更新</button>
          <span class="auto-indicator"><span class="live-dot" aria-hidden="true"></span>自動更新中（3秒）</span>
        </div>
      </header>

      <div class="tab-panels">
        <div class="tab-panel active" data-panel="overview">
          <section id="connect-card" class="connect-card" hidden>
            <div class="section-head"><h2>接続</h2></div>
            <p class="connect-hint">Web UI トークンを入力すると操作・設定ができます。トークンは Pi の <code>config/secrets.json</code> に保存されています。</p>
            <div class="connect-row">
              <input id="token" type="password" autocomplete="current-password" placeholder="Web UI Token">
              <button onclick="saveTokenAndConnect()">保存して接続</button>
            </div>
          </section>
          <div class="overview-grid">
            <div class="overview-sidebar">
              <section>
                <div class="section-head"><h2>次のアラーム</h2><span id="scheduled-alarm-state" class="pill off">OFF</span></div>
                <div class="alarm-summary">
                  <strong id="scheduled-alarm-next">次のアラームは未設定です。</strong>
                </div>
                <div id="alarm-preview-list" class="alarm-preview-list"></div>
                <button class="link-button" type="button" onclick="showTab('alarms')">アラームを管理</button>
              </section>

              <section>
                <div class="section-head"><h2>最近のできごと</h2></div>
                <div id="event-timeline" class="timeline">
                  <p class="timeline-empty">状態の変化がここに記録されます。</p>
                </div>
              </section>
            </div>

            <section class="overview-status" id="status-panel">
              <div class="section-head">
                <h2>状態</h2>
                <span id="status-time" class="pill off">未取得</span>
              </div>
              <div class="status-cards">
                <div class="metric"><span>状態</span><strong id="metric-state">-</strong></div>
                <div class="metric"><span>イベント</span><strong id="metric-event">-</strong></div>
                <div class="metric"><span>重量</span><strong id="metric-weight">-</strong></div>
                <div class="metric"><span>プロセス</span><strong id="metric-process">-</strong></div>
                <div class="metric"><span>次アラーム</span><strong id="metric-next-alarm">-</strong></div>
                <div class="metric"><span>再確認</span><strong id="metric-recheck">-</strong></div>
              </div>
              <details class="status-details">
                <summary>詳細データ（JSON）</summary>
                <pre id="status" class="status">未取得</pre>
              </details>
            </section>
          </div>
        </div>

        <div class="tab-panel" data-panel="alarms">
          <div class="stack" id="alarms">
          <section>
            <div class="section-head"><h2>時刻アラーム</h2><span id="scheduled-alarm-pill" class="pill off">OFF</span></div>
            <div class="alarm-card">
              <div>
                <strong>複数アラーム</strong>
                <span id="scheduled-alarm-next-line">設定時刻にベッド上ならアラーム。起床ミッションONなら離床し続けるまで再アラームします。</span>
              </div>
              <label class="switch" aria-label="時刻アラーム">
                <input id="quick_scheduled_alarm_enabled" type="checkbox" onchange="toggleScheduledAlarm(this.checked)">
                <span class="slider"></span>
              </label>
            </div>
            <button class="link-button" type="button" onclick="showTab('settings')">アラームを編集</button>
          </section>

          <section>
            <div class="section-head"><h2>二度寝検知アラーム</h2><span id="alarm-pill" class="pill off">OFF</span></div>
            <div class="alarm-card">
              <div>
                <strong>アラーム</strong>
                <span>ONにすると二度寝検知時にDiscord通知とブザーを鳴らします。</span>
              </div>
              <label class="switch" aria-label="二度寝アラーム">
                <input id="quick_alarm_enabled" type="checkbox" onchange="toggleAlarm(this.checked)">
                <span class="slider"></span>
              </label>
            </div>
          </section>
          </div>
        </div>

        <div class="tab-panel" data-panel="calibration">
          <section id="calibration-panel">
            <div class="section-head"><h2>キャリブレーション</h2></div>
            <div class="grid">
              <label>サンプル数<input id="cal_samples" type="number" value="30" min="1"></label>
              <label>既知重量 kg<input id="known_kg" type="number" step="0.1" min="0"></label>
            </div>
            <div class="actions">
              <button class="secondary" onclick="checkSensor(event)">センサー確認</button>
              <button onclick="calibrateZero(event)">ゼロ校正</button>
              <button onclick="calibrateScale(event)">重量校正</button>
            </div>
            <div id="sensor-check-result" class="sensor-check-result">未確認</div>
          </section>
        </div>

        <section class="tab-panel" data-panel="settings" id="settings-panel">
          <div class="section-head sticky">
            <h2>設定</h2>
            <div class="actions">
              <button onclick="saveSettings(event)">設定を保存</button>
              <button class="secondary" onclick="post('/api/test-webhook')">Webhookテスト</button>
            </div>
          </div>
          <div id="settings" class="grid settings-grid"></div>
          <div class="mobile-save-bar">
            <button class="secondary" onclick="post('/api/test-webhook')">Webhookテスト</button>
            <button onclick="saveSettings(event)">設定を保存</button>
          </div>
        </section>
      </div>
    </div>
  </div>
  <p id="message" class="message"></p>
</main>
<script>
const fields = [
  ['log_path','text'], ['status_path','text'], ['person_weight_kg','number'],
  ['sample_interval_sec','number'], ['warmup_samples','number'], ['median_samples','number'],
  ['moving_average_window','number'], ['exit_ratio','number'], ['return_ratio','number'],
  ['monitor_sec','number'], ['confirm_sec','number'], ['data_pin','text'], ['clock_pin','text'],
  ['hx711_ready_timeout_sec','number'], ['alarm_enabled','checkbox'], ['buzzer_enabled','checkbox'],
  ['buzzer_pin','text'], ['buzzer_duration_sec','number'], ['buzzer_pulse_sec','number'],
  ['scheduled_alarm_enabled','checkbox'], ['bed_recheck_minutes','number'],
  ['wake_mission_enabled','checkbox'], ['wake_mission_required_off_bed_sec','number'],
  ['webhook_enabled','checkbox'], ['webhook_events','text'],
  ['webhook_payload_format','select'], ['webhook_timeout_sec','number'], ['webhook_url','password']
];
// [タイトル, グループ説明, 基本フィールド, 詳細フィールド(折りたたみ)]
const fieldGroups = [
  ['基本', '就寝者の体重とサンプリングの基本設定。',
    ['person_weight_kg', 'sample_interval_sec'], ['log_path', 'status_path']],
  ['検知', '離床・再入床・二度寝を判定するしきい値と時間。',
    ['exit_ratio', 'return_ratio', 'monitor_sec', 'confirm_sec', 'moving_average_window'], []],
  ['センサー', 'HX711ロードセルの読み取りとGPIO配線。通常は変更不要。',
    [], ['warmup_samples', 'median_samples', 'data_pin', 'clock_pin', 'hx711_ready_timeout_sec']],
  ['時刻アラーム', '指定時刻にベッド上ならアラーム。起床ミッションで離床を促す。',
    ['scheduled_alarm_enabled', 'bed_recheck_minutes', 'wake_mission_enabled', 'wake_mission_required_off_bed_sec', 'scheduled_alarms'], []],
  ['二度寝検知アラーム', '二度寝を検知したときのブザーと通知。',
    ['alarm_enabled', 'buzzer_enabled', 'buzzer_duration_sec', 'webhook_url'], ['buzzer_pin', 'buzzer_pulse_sec']],
  ['通知', 'Discord等へのWebhook通知の送信設定。',
    ['webhook_enabled', 'webhook_events', 'webhook_payload_format'], ['webhook_timeout_sec']]
];
const fieldTypes = Object.fromEntries(fields);
const weekdayLabels = ['月', '火', '水', '木', '金', '土', '日'];
const fieldLabels = {
  log_path: 'ログ',
  status_path: '状態ファイル',
  person_weight_kg: '体重 kg',
  sample_interval_sec: '読取間隔 秒',
  warmup_samples: 'ウォームアップ',
  median_samples: '中央値サンプル',
  moving_average_window: '平滑化',
  exit_ratio: '離床しきい値',
  return_ratio: '入床しきい値',
  monitor_sec: '監視時間 秒',
  confirm_sec: '確認時間 秒',
  data_pin: 'DATAピン',
  clock_pin: 'CLOCKピン',
  hx711_ready_timeout_sec: 'HX711待機 秒',
  alarm_enabled: '二度寝検知',
  buzzer_enabled: 'ブザー',
  buzzer_pin: 'ブザーピン',
  buzzer_duration_sec: '鳴動時間 秒',
  buzzer_pulse_sec: 'パルス 秒',
  scheduled_alarm_enabled: '時刻アラーム',
  bed_recheck_minutes: '再確認 分',
  wake_mission_enabled: '起床ミッション',
  wake_mission_required_off_bed_sec: '離床確認 秒',
  webhook_enabled: 'Webhook',
  webhook_events: '通知イベント',
  webhook_payload_format: '形式',
  webhook_timeout_sec: 'タイムアウト 秒',
  webhook_url: 'Webhook URL'
};
const fieldHelp = {
  log_path: 'CSVログの保存先パス',
  status_path: '現在状態を書き出すJSONファイル',
  person_weight_kg: '就寝者の体重。離床/入床の判定基準（kg）',
  sample_interval_sec: '重量を読み取る間隔（秒）',
  warmup_samples: '起動直後に捨てるサンプル数',
  median_samples: '1回の読み取りで中央値をとるサンプル数',
  moving_average_window: '重量を平滑化する移動平均の点数',
  exit_ratio: '体重比がこれ未満で離床と判定（0〜1）',
  return_ratio: '体重比がこれ以上で再入床と判定（exitより大きく）',
  monitor_sec: '離床後に二度寝を監視する時間（秒）',
  confirm_sec: '再入床が続いたら二度寝確定とする時間（秒）',
  data_pin: 'HX711 DATA(DT)に接続したGPIOピン',
  clock_pin: 'HX711 CLOCK(SCK)に接続したGPIOピン',
  hx711_ready_timeout_sec: 'HX711の応答待ちタイムアウト（秒）',
  alarm_enabled: '二度寝検知時にブザー/通知を出す',
  buzzer_enabled: 'ブザーを鳴らす',
  buzzer_pin: 'ブザーを接続したGPIOピン',
  buzzer_duration_sec: 'ブザーの最大鳴動時間（秒）',
  buzzer_pulse_sec: 'ブザーのON/OFF間隔（秒）',
  scheduled_alarm_enabled: '時刻アラーム全体のON/OFF',
  bed_recheck_minutes: 'アラーム後にベッドを再確認する間隔（分）',
  wake_mission_enabled: '離床し続けるまで再アラームする',
  wake_mission_required_off_bed_sec: 'ミッション達成に必要な離床継続（秒）',
  webhook_enabled: 'Webhook通知を送る',
  webhook_events: '通知するイベント名（カンマ区切り）',
  webhook_payload_format: '送信形式（discord または json）',
  webhook_timeout_sec: 'Webhook送信のタイムアウト（秒）',
  webhook_url: '通知先のWebhook URL（Discord等）'
};
let current = {};
let weightHistory = [];
let eventLog = [];
let lastEventKey = null;
let messageTimer = null;

function applyTheme(theme) {
  const chosen = theme === 'dark' ? 'dark' : 'light';
  document.documentElement.dataset.theme = chosen;
  const icon = document.getElementById('theme-icon');
  const label = document.getElementById('theme-label');
  const toggle = document.getElementById('theme-toggle');
  if (icon) icon.textContent = chosen === 'dark' ? '☾' : '☀';
  if (label) label.textContent = chosen === 'dark' ? 'Dark' : 'Light';
  if (toggle) toggle.setAttribute('aria-pressed', chosen === 'dark' ? 'true' : 'false');
}

function initTheme() {
  const saved = localStorage.getItem('twodosumi_theme');
  const preferred = window.matchMedia && window.matchMedia('(prefers-color-scheme: dark)').matches ? 'dark' : 'light';
  applyTheme(saved || preferred);
}

function toggleTheme() {
  const next = document.documentElement.dataset.theme === 'dark' ? 'light' : 'dark';
  localStorage.setItem('twodosumi_theme', next);
  applyTheme(next);
  note(next === 'dark' ? 'ダークモードに切り替えました' : 'ライトモードに切り替えました');
}

function showTab(name) {
  document.body.dataset.tab = name;
  document.querySelectorAll('.tab-button').forEach(button => {
    const active = button.dataset.tab === name;
    button.classList.toggle('active', active);
    button.setAttribute('aria-selected', active ? 'true' : 'false');
  });
  document.querySelectorAll('.tab-panel').forEach(panel => {
    panel.classList.toggle('active', panel.dataset.panel === name);
  });
  history.replaceState(null, '', `#${name}`);
}

function initTabs() {
  document.querySelectorAll('.tab-button').forEach(button => {
    button.addEventListener('click', () => showTab(button.dataset.tab || 'overview'));
  });
  const initial = (location.hash || '#overview').replace('#', '');
  const exists = document.querySelector(`.tab-panel[data-panel="${initial}"]`);
  showTab(exists ? initial : 'overview');
}

const stateMeta = {
  SLEEPING: {label: '在床', tone: 'sleep'},
  AWAKE_WINDOW: {label: '離床・監視中', tone: 'watch'},
  RETURNED: {label: '再入床', tone: 'watch'},
  SECOND_SLEEP: {label: '二度寝検知', tone: 'alert'},
  DONE: {label: '起床完了', tone: 'done'}
};

function token() { return localStorage.getItem('twodosumi_token') || document.getElementById('token').value; }
function saveToken() { localStorage.setItem('twodosumi_token', document.getElementById('token').value); note('トークンを保存しました'); }

function updateAuthChip() {
  const authed = Boolean(token());
  const chip = document.getElementById('auth-chip');
  if (!chip) return;
  chip.textContent = authed ? '認証済' : '未認証';
  chip.classList.toggle('off', !authed);
}

function showConnect() {
  showTab('overview');
  const card = document.getElementById('connect-card');
  if (card) card.hidden = false;
  const input = document.getElementById('token');
  if (input) { input.value = token(); input.focus(); }
}

async function saveTokenAndConnect() {
  saveToken();
  updateAuthChip();
  await loadSettings();
  loadStatus();
}

function note(text, type) {
  const el = document.getElementById('message');
  el.textContent = text;
  el.classList.remove('ok', 'error');
  if (type) el.classList.add(type);
  el.classList.add('show');
  clearTimeout(messageTimer);
  messageTimer = setTimeout(() => el.classList.remove('show'), 3600);
}

async function withBusy(btn, busyLabel, fn) {
  const original = btn ? btn.innerHTML : null;
  if (btn) { btn.disabled = true; btn.innerHTML = `<span class="spinner"></span>${busyLabel}`; }
  try { return await fn(); }
  finally { if (btn) { btn.disabled = false; btn.innerHTML = original; } }
}
function headers() { return {'Content-Type': 'application/json', 'X-2Dosumi-Token': token()}; }

async function api(path, opts={}) {
  const res = await fetch(path, {...opts, headers: headers()});
  const data = await res.json();
  if (!data.ok) throw new Error(data.error || 'request failed');
  return data;
}

function renderSettings(settings) {
  current = settings;
  syncAlarmUi(Boolean(settings.alarm_enabled));
  syncScheduledAlarmUi(Boolean(settings.scheduled_alarm_enabled));
  renderAlarmPreview(settings.scheduled_alarms || []);
  const root = document.getElementById('settings');
  root.innerHTML = '';
  const addField = (target, name) => {
    if (name === 'scheduled_alarms') target.appendChild(createScheduledAlarmEditor(settings.scheduled_alarms || []));
    else target.appendChild(createSettingField(name, fieldTypes[name], settings));
  };
  for (const [title, desc, basic, advanced] of fieldGroups) {
    const group = document.createElement('div');
    group.className = 'setting-group';
    if (basic.includes('scheduled_alarms') || (advanced || []).includes('scheduled_alarms')) group.classList.add('wide');
    const heading = document.createElement('h3');
    heading.textContent = title;
    group.appendChild(heading);
    if (desc) {
      const descEl = document.createElement('p');
      descEl.className = 'group-desc';
      descEl.textContent = desc;
      group.appendChild(descEl);
    }
    if (basic.length) {
      const fieldsRoot = document.createElement('div');
      fieldsRoot.className = 'setting-group-fields';
      for (const name of basic) addField(fieldsRoot, name);
      group.appendChild(fieldsRoot);
    }
    if ((advanced || []).length) {
      const details = document.createElement('details');
      details.className = 'group-advanced';
      const summary = document.createElement('summary');
      summary.textContent = '詳細設定';
      const advFields = document.createElement('div');
      advFields.className = 'setting-group-fields';
      for (const name of advanced) addField(advFields, name);
      details.appendChild(summary);
      details.appendChild(advFields);
      group.appendChild(details);
    }
    root.appendChild(group);
  }
}

function renderAlarmPreview(alarms) {
  const root = document.getElementById('alarm-preview-list');
  if (!root) return;
  root.innerHTML = '';
  const shown = alarms.filter(alarm => alarm.enabled !== false).slice(0, 3);
  if (!shown.length) {
    const empty = document.createElement('div');
    empty.className = 'alarm-preview-item';
    empty.innerHTML = '<span class="alarm-preview-time">--:--</span><span class="alarm-preview-meta"><strong>未設定</strong><span>アラームを追加してください</span></span><span class="pill off">OFF</span>';
    root.appendChild(empty);
    return;
  }
  for (const alarm of shown) {
    const item = document.createElement('div');
    item.className = 'alarm-preview-item';
    const days = (alarm.weekdays || []).map(day => weekdayLabels[day]).filter(Boolean).join(' ');
    item.innerHTML = `
      <span class="alarm-preview-time">${alarm.time || '--:--'}</span>
      <span class="alarm-preview-meta">
        <strong>${escapeHtml(alarm.label || 'アラーム')}</strong>
        <span>${days || '曜日未設定'}</span>
      </span>
      <span class="pill">ON</span>
    `;
    root.appendChild(item);
  }
}

function escapeHtml(value) {
  return String(value).replace(/[&<>"']/g, char => ({
    '&': '&amp;',
    '<': '&lt;',
    '>': '&gt;',
    '"': '&quot;',
    "'": '&#39;'
  }[char]));
}

function syncAlarmUi(enabled) {
  const alarmInput = document.getElementById('quick_alarm_enabled');
  const alarmPill = document.getElementById('alarm-pill');
  if (alarmInput) alarmInput.checked = enabled;
  if (alarmPill) {
    alarmPill.textContent = enabled ? 'ON' : 'OFF';
    alarmPill.classList.toggle('off', !enabled);
  }
}

async function toggleAlarm(enabled) {
  try {
    await api('/api/settings', {method: 'POST', body: JSON.stringify({settings: {alarm_enabled: enabled}})});
    current.alarm_enabled = enabled;
    syncAlarmUi(enabled);
    const fullField = document.getElementById('set_alarm_enabled');
    if (fullField) fullField.checked = enabled;
    note(enabled ? '二度寝アラームを有効化しました' : '二度寝アラームを無効化しました');
  } catch (err) {
    syncAlarmUi(Boolean(current.alarm_enabled));
    note(err.message, 'error');
  }
}

function syncScheduledAlarmUi(enabled) {
  const input = document.getElementById('quick_scheduled_alarm_enabled');
  if (input) input.checked = enabled;
  for (const badge of document.querySelectorAll('#scheduled-alarm-pill, #scheduled-alarm-state')) {
    badge.textContent = enabled ? 'ON' : 'OFF';
    badge.classList.toggle('off', !enabled);
  }
}

async function toggleScheduledAlarm(enabled) {
  try {
    await api('/api/settings', {method: 'POST', body: JSON.stringify({settings: {scheduled_alarm_enabled: enabled}})});
    current.scheduled_alarm_enabled = enabled;
    syncScheduledAlarmUi(enabled);
    const fullField = document.getElementById('set_scheduled_alarm_enabled');
    if (fullField) fullField.checked = enabled;
    note(enabled ? '時刻アラームを有効化しました' : '時刻アラームを無効化しました');
  } catch (err) {
    syncScheduledAlarmUi(Boolean(current.scheduled_alarm_enabled));
    note(err.message, 'error');
  }
}

function createSettingField(name, type, settings) {
    const label = document.createElement('label');
    label.textContent = fieldLabels[name] || name;
    let input;
    if (name === 'webhook_payload_format') {
      input = document.createElement('select');
      for (const value of ['discord', 'json']) {
        const opt = document.createElement('option');
        opt.value = value; opt.textContent = value; input.appendChild(opt);
      }
    } else {
      input = document.createElement('input');
      input.type = type;
      if (type === 'number') input.step = 'any';
    }
    input.id = 'set_' + name;
    if (name === 'webhook_events') input.value = (settings[name] || []).join(',');
    else if (type === 'checkbox') input.checked = Boolean(settings[name]);
    else input.value = settings[name] ?? '';
    label.appendChild(input);
    if (fieldHelp[name]) {
      const help = document.createElement('small');
      help.className = 'field-help';
      help.textContent = fieldHelp[name];
      label.appendChild(help);
    }
    return label;
}

function createScheduledAlarmEditor(alarms) {
  const wrap = document.createElement('div');
  wrap.className = 'scheduled-editor full';
  wrap.id = 'scheduled_alarm_editor';
  for (const alarm of alarms) wrap.appendChild(createScheduledAlarmRow(alarm));
  const add = document.createElement('button');
  add.type = 'button';
  add.className = 'secondary';
  add.textContent = 'アラームを追加';
  add.onclick = () => addScheduledAlarm();
  wrap.appendChild(add);
  return wrap;
}

function createScheduledAlarmRow(alarm) {
  const row = document.createElement('div');
  row.className = 'scheduled-row';
  row.dataset.id = alarm.id || `alarm_${Date.now()}`;

  const timeBlock = document.createElement('div');
  timeBlock.className = 'scheduled-time-block';
  const enabled = document.createElement('label');
  enabled.className = 'switch';
  enabled.setAttribute('aria-label', 'アラーム');
  const enabledInput = document.createElement('input');
  enabledInput.className = 'scheduled-enabled';
  enabledInput.type = 'checkbox';
  enabledInput.checked = alarm.enabled !== false;
  const enabledSlider = document.createElement('span');
  enabledSlider.className = 'slider';
  enabled.appendChild(enabledInput);
  enabled.appendChild(enabledSlider);

  const timeInput = document.createElement('input');
  timeInput.className = 'scheduled-time';
  timeInput.type = 'time';
  timeInput.value = alarm.time || '07:00';
  timeBlock.appendChild(enabled);
  timeBlock.appendChild(timeInput);

  const detail = document.createElement('div');
  detail.className = 'scheduled-detail';
  const labelInput = document.createElement('input');
  labelInput.className = 'scheduled-label';
  labelInput.type = 'text';
  labelInput.placeholder = 'ラベル';
  labelInput.value = alarm.label || '';

  const weekdays = document.createElement('div');
  weekdays.className = 'weekday-row';
  const selected = new Set(alarm.weekdays || [0, 1, 2, 3, 4, 5, 6]);
  for (let day = 0; day < 7; day += 1) {
    const dayLabel = document.createElement('label');
    const dayInput = document.createElement('input');
    dayInput.type = 'checkbox';
    dayInput.className = 'scheduled-weekday';
    dayInput.value = String(day);
    dayInput.checked = selected.has(day);
    dayLabel.appendChild(dayInput);
    dayLabel.appendChild(document.createTextNode(weekdayLabels[day]));
    weekdays.appendChild(dayLabel);
  }
  detail.appendChild(labelInput);
  detail.appendChild(weekdays);

  const remove = document.createElement('button');
  remove.type = 'button';
  remove.className = 'warn';
  remove.textContent = '削除';
  remove.onclick = () => row.remove();

  row.appendChild(timeBlock);
  row.appendChild(detail);
  row.appendChild(remove);
  return row;
}

function addScheduledAlarm() {
  const editor = document.getElementById('scheduled_alarm_editor');
  if (!editor) return;
  const button = editor.querySelector('button.secondary');
  const row = createScheduledAlarmRow({
    id: `alarm_${Date.now()}`,
    time: '07:00',
    enabled: true,
    label: '',
    weekdays: [0, 1, 2, 3, 4, 5, 6]
  });
  editor.insertBefore(row, button);
}

function collectScheduledAlarms() {
  return [...document.querySelectorAll('.scheduled-row')].map(row => ({
    id: row.dataset.id,
    time: row.querySelector('.scheduled-time').value || '07:00',
    enabled: row.querySelector('.scheduled-enabled').checked,
    label: row.querySelector('.scheduled-label').value,
    weekdays: [...row.querySelectorAll('.scheduled-weekday:checked')].map(el => Number(el.value))
  }));
}

async function loadSettings() {
  try {
    document.getElementById('token').value = token();
    const data = await api('/api/settings');
    renderSettings(data.settings);
    const card = document.getElementById('connect-card');
    if (card) card.hidden = true;
    updateAuthChip();
    note('設定を読み込みました');
  } catch (err) { note(err.message, 'error'); }
}

async function saveSettings(ev) {
  const btn = ev && ev.currentTarget;
  await withBusy(btn, '保存中', async () => {
    try {
      const settings = {};
      for (const [name, type] of fields) {
        const el = document.getElementById('set_' + name);
        if (name === 'webhook_events') settings[name] = el.value.split(',').map(v => v.trim()).filter(Boolean);
        else if (type === 'checkbox') settings[name] = el.checked;
        else if (type === 'number') settings[name] = Number(el.value);
        else settings[name] = el.value;
      }
      settings.scheduled_alarms = collectScheduledAlarms();
      await api('/api/settings', {method: 'POST', body: JSON.stringify({settings})});
      current = {...current, ...settings};
      renderAlarmPreview(settings.scheduled_alarms);
      note('設定を保存しました', 'ok');
    } catch (err) { note(err.message, 'error'); }
  });
}

function setText(id, value) { document.getElementById(id).textContent = value || '-'; }
function formatAlarm(alarm) {
  if (!alarm) return '-';
  const label = alarm.label ? ` ${alarm.label}` : '';
  return `${alarm.time}${label}`;
}
function activeRecheck(rechecks) {
  return rechecks.reduce((best, r) =>
    Number(r.off_bed_elapsed_sec || 0) > Number(best.off_bed_elapsed_sec || 0) ? r : best
  );
}

function applyHeroState(state) {
  const badge = document.getElementById('hero-state-badge');
  if (!badge) return;
  const meta = stateMeta[state];
  badge.textContent = meta ? meta.label : (state || '未取得');
  badge.className = 'state-badge ' + (meta ? 'state-' + meta.tone : 'state-idle');
}

function updateMission(rechecks) {
  const box = document.getElementById('hero-mission');
  if (!box) return;
  if (!rechecks.length) { box.hidden = true; return; }
  const active = activeRecheck(rechecks);
  const elapsed = Math.floor(Number(active.off_bed_elapsed_sec || 0));
  const required = Math.floor(Number(active.required_off_bed_sec || 0));
  const count = Number(active.realarm_count || 0);
  box.hidden = false;
  const labelEl = document.getElementById('hero-mission-label');
  const valEl = document.getElementById('hero-mission-value');
  const bar = document.getElementById('hero-mission-bar');
  if (required > 0) {
    labelEl.textContent = '起床ミッション（離床を継続）';
    const pct = Math.max(0, Math.min(100, (elapsed / required) * 100));
    bar.style.width = pct + '%';
    valEl.textContent = `${elapsed} / ${required} 秒`;
  } else {
    labelEl.textContent = '再アラーム中';
    bar.style.width = '100%';
    valEl.textContent = count ? `${count} 回` : '進行中';
  }
}

function updateStatusView(status) {
  const running = Boolean(status.managed_process_running || status.running);
  const runPill = document.getElementById('run-pill');
  runPill.textContent = running ? '稼働中' : '停止中';
  runPill.classList.toggle('off', !running);
  const timePill = document.getElementById('status-time');
  timePill.textContent = status.timestamp || '未取得';
  timePill.classList.toggle('off', !status.timestamp);
  setText('metric-state', stateMeta[status.state] ? stateMeta[status.state].label : status.state);
  setText('metric-event', status.event);
  const weight = status.smoothed_weight_kg == null ? '-' : `${Number(status.smoothed_weight_kg).toFixed(2)} kg`;
  setText('metric-weight', weight);
  setText('metric-process', running ? '稼働中' : '停止中');
  setText('metric-next-alarm', formatAlarm(status.next_scheduled_alarm));
  const rechecks = status.pending_rechecks || [];
  setText('metric-recheck', formatRechecks(rechecks));
  setText('scheduled-alarm-next', status.next_scheduled_alarm ? `次: ${formatAlarm(status.next_scheduled_alarm)}` : '次のアラームは未設定です。');
  applyHeroState(status.state);
  updateMission(rechecks);
  setText('hero-weight', weight);
  const updated = document.getElementById('hero-updated');
  if (updated) updated.textContent = status.timestamp ? `更新 ${status.timestamp}` : '更新待ち';
  document.getElementById('status').textContent = JSON.stringify(status, null, 2);
  applyMetricTone(status.state);
  pushWeight(status.smoothed_weight_kg);
  trackEvent(status);
}

function applyMetricTone(state) {
  const card = document.getElementById('metric-state');
  if (!card) return;
  const metric = card.closest('.metric');
  if (metric) metric.dataset.tone = stateMeta[state] ? stateMeta[state].tone : 'idle';
}

function pushWeight(value) {
  if (value == null || Number.isNaN(Number(value))) return;
  weightHistory.push(Number(value));
  if (weightHistory.length > 60) weightHistory.shift();
  renderSparkline();
}

function renderSparkline() {
  const trend = document.getElementById('hero-trend');
  const line = document.getElementById('sparkline-line');
  const area = document.getElementById('sparkline-area');
  const dot = document.getElementById('sparkline-dot');
  const caption = document.getElementById('trend-caption');
  if (!trend || !line) return;
  if (weightHistory.length < 2) { trend.classList.add('empty'); return; }
  trend.classList.remove('empty');
  const W = 300, H = 56, pad = 4;
  const min = Math.min(...weightHistory);
  const max = Math.max(...weightHistory);
  const span = (max - min) || 1;
  const n = weightHistory.length;
  const px = i => pad + (i / (n - 1)) * (W - pad * 2);
  const py = v => H - pad - ((v - min) / span) * (H - pad * 2);
  const pts = weightHistory.map((v, i) => `${px(i).toFixed(1)},${py(v).toFixed(1)}`);
  line.setAttribute('points', pts.join(' '));
  area.setAttribute('points', `${pad},${H} ${pts.join(' ')} ${W - pad},${H}`);
  dot.setAttribute('cx', px(n - 1).toFixed(1));
  dot.setAttribute('cy', py(weightHistory[n - 1]).toFixed(1));
  dot.hidden = false;
  if (caption) caption.textContent = `重量の推移（直近${n}点）  ${min.toFixed(1)}〜${max.toFixed(1)} kg`;
}

function shortTime(ts) {
  if (ts && ts.includes(' ')) return ts.split(' ')[1].slice(0, 5);
  if (ts && ts.includes('T')) return ts.split('T')[1].slice(0, 5);
  const d = new Date();
  return `${String(d.getHours()).padStart(2, '0')}:${String(d.getMinutes()).padStart(2, '0')}`;
}

function trackEvent(status) {
  const sig = `${status.state || ''}|${status.event || ''}`;
  if (sig === '|' || sig === lastEventKey) return;
  lastEventKey = sig;
  const meta = stateMeta[status.state];
  eventLog.unshift({
    label: meta ? meta.label : (status.event || status.state || '更新'),
    detail: status.event || '',
    tone: meta ? meta.tone : 'idle',
    time: shortTime(status.timestamp)
  });
  if (eventLog.length > 20) eventLog.pop();
  renderTimeline();
}

function renderTimeline() {
  const root = document.getElementById('event-timeline');
  if (!root) return;
  if (!eventLog.length) {
    root.innerHTML = '<p class="timeline-empty">状態の変化がここに記録されます。</p>';
    return;
  }
  root.innerHTML = '';
  for (const entry of eventLog) {
    const item = document.createElement('div');
    item.className = 'event-item';
    const dot = document.createElement('span');
    dot.className = 'event-dot tone-' + entry.tone;
    const label = document.createElement('span');
    label.className = 'event-label';
    label.textContent = entry.label;
    if (entry.detail) label.title = entry.detail;
    const time = document.createElement('span');
    time.className = 'event-time';
    time.textContent = entry.time;
    item.appendChild(dot);
    item.appendChild(label);
    item.appendChild(time);
    root.appendChild(item);
  }
}

function formatRechecks(rechecks) {
  if (!rechecks.length) return '-';
  const suffix = rechecks.length > 1 ? ` (+${rechecks.length - 1})` : '';
  const active = activeRecheck(rechecks);
  const elapsed = Math.floor(Number(active.off_bed_elapsed_sec || 0));
  const required = Math.floor(Number(active.required_off_bed_sec || 0));
  const count = Number(active.realarm_count || 0);
  if (elapsed > 0 && required > 0) return `離床 ${elapsed}/${required}秒${suffix}`;
  return count ? `再アラーム ${count}回${suffix}` : `${rechecks.length}件 待機`;
}

async function loadStatus() {
  if (!token()) return;
  try {
    const data = await api('/api/status');
    updateStatusView(data.status);
  } catch (err) { note(err.message, 'error'); }
}

async function post(path, body={}) {
  try {
    const data = await api(path, {method: 'POST', body: JSON.stringify(body)});
    note('実行しました', 'ok');
    loadStatus();
    return data;
  } catch (err) { note(err.message, 'error'); }
}

function calibrateZero(ev) {
  return withBusy(ev && ev.currentTarget, '校正中', () =>
    post('/api/calibration/zero', {samples: Number(document.getElementById('cal_samples').value)})
  );
}
function calibrateScale(ev) {
  return withBusy(ev && ev.currentTarget, '校正中', () =>
    post('/api/calibration/scale', {
      samples: Number(document.getElementById('cal_samples').value),
      known_kg: Number(document.getElementById('known_kg').value)
    })
  );
}

async function checkSensor(ev) {
  const btn = ev && ev.currentTarget;
  await withBusy(btn, '確認中', async () => {
    const root = document.getElementById('sensor-check-result');
    root.className = 'sensor-check-result';
    root.textContent = '確認中...';
    try {
      const data = await api('/api/sensor/check', {
        method: 'POST',
        body: JSON.stringify({
          samples: Number(document.getElementById('cal_samples').value) || 10,
          interval_sec: 0.1
        })
      });
      renderSensorCheck(data.sensor, data.restarted);
      note(data.sensor.ok ? 'センサー確認: OK' : 'センサー確認: NG', data.sensor.ok ? 'ok' : 'error');
    } catch (err) {
      root.className = 'sensor-check-result fail';
      root.textContent = err.message;
      note(err.message, 'error');
    }
  });
}

function renderSensorCheck(sensor, restarted) {
  const root = document.getElementById('sensor-check-result');
  root.className = `sensor-check-result ${sensor.ok ? 'ok' : 'fail'}`;
  const lines = [
    `${sensor.ok ? 'OK' : 'NG'}: ${sensor.message || ''}`,
    `reader: ${sensor.reader}`,
    `samples: ${sensor.samples_read}/${sensor.samples_requested}`,
    `duration: ${Number(sensor.duration_sec || 0).toFixed(2)} sec`
  ];
  if (sensor.raw_median != null) {
    lines.push(
      `raw: min=${Number(sensor.raw_min).toFixed(3)} max=${Number(sensor.raw_max).toFixed(3)} median=${Number(sensor.raw_median).toFixed(3)} span=${Number(sensor.raw_span).toFixed(3)}`
    );
  }
  if (sensor.weight_median_kg != null) {
    lines.push(`weight median: ${Number(sensor.weight_median_kg).toFixed(3)} kg`);
  }
  for (const warning of sensor.warnings || []) {
    lines.push(`WARNING: ${warning}`);
  }
  if (restarted) lines.push('検知プロセスを一時停止して再開しました。');
  root.textContent = lines.join('\n');
}

initTheme();
initTabs();
updateAuthChip();
setInterval(loadStatus, 3000);
document.getElementById('token').value = token();
if (token()) { loadSettings(); loadStatus(); }
else { showConnect(); note('Web UI トークンを入力してください'); }
</script>
</body>
</html>
"""
